ElectronicCats/CatFinder/Mechanics/SolidWorks/caramelo.SLDPRT

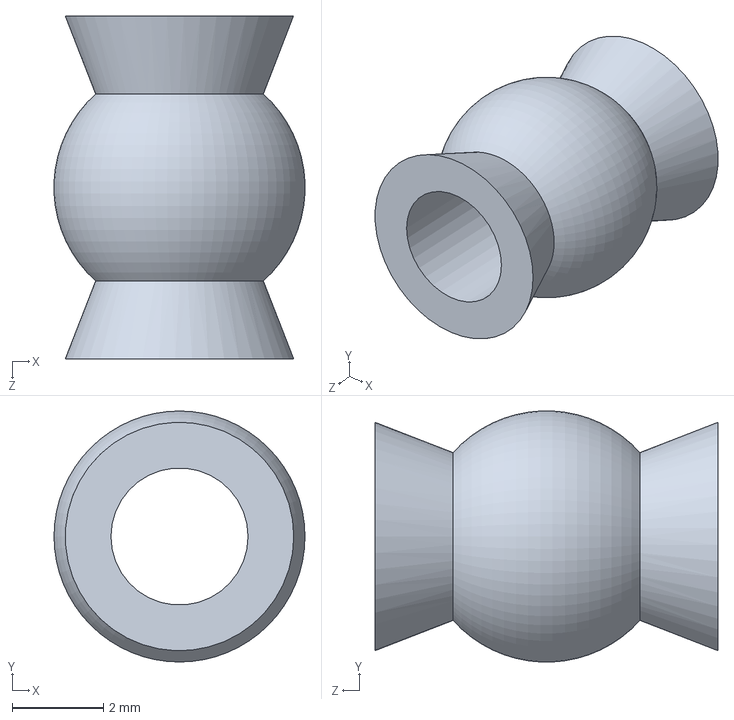
[picture p13: CAD file, 2019-09-29]
Mechanics/SolidWorks/caramelo.SLDPRT
5.49 x 5.49 x 7.50 mm
