ElectronicCats/CatFinder/Mechanics/SolidWorks/Acrilico frontal.SLDPRT

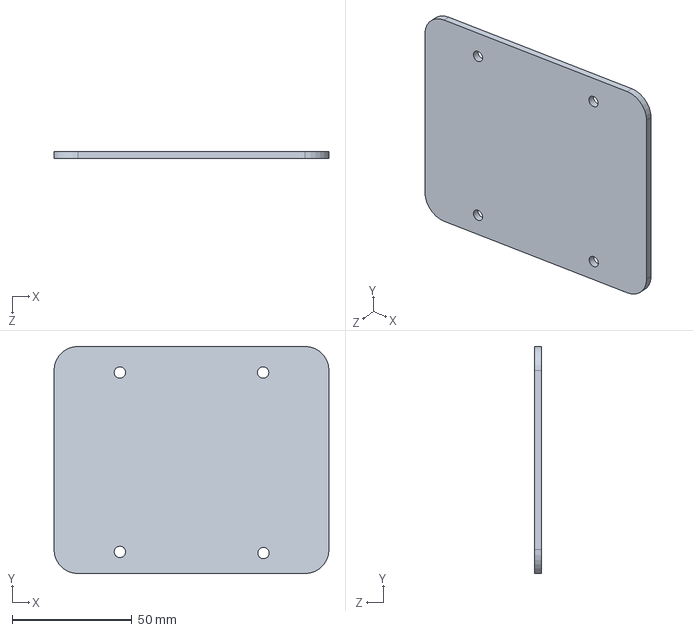
[picture p14: CAD file, 2019-09-29]
Mechanics/SolidWorks/Acrilico frontal.SLDPRT
115.0 x 95.0 x 3.00 mm
