ElectronicCats/CatFinder/Mechanics/SolidWorks/Soporte shf8.SLDPRT

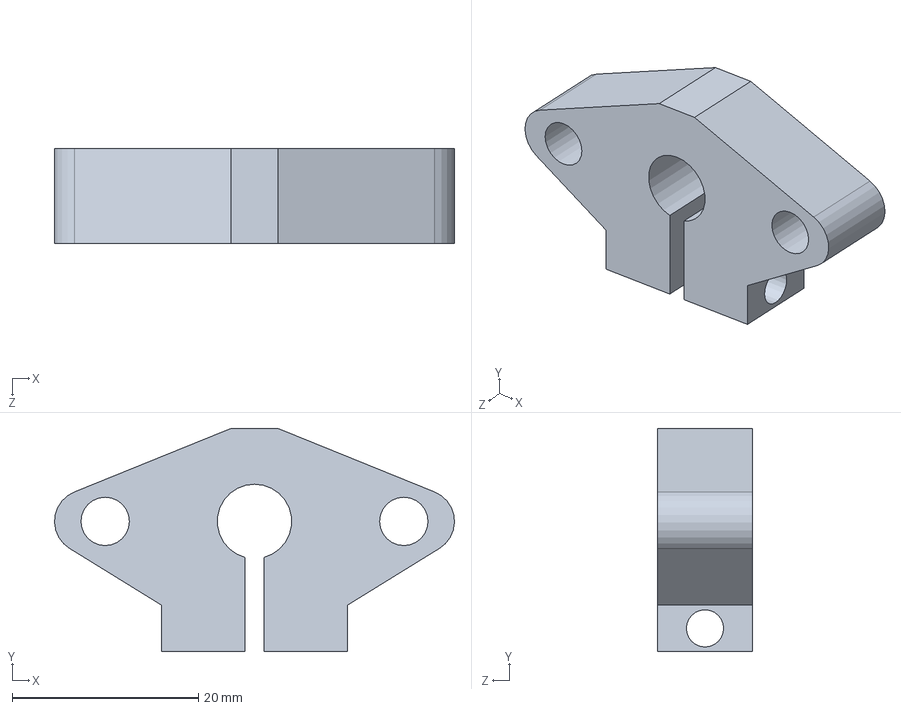
[picture p15: CAD file, 2019-09-29]
Mechanics/SolidWorks/Soporte shf8.SLDPRT
43.0 x 24.0 x 10.2 mm
