ElectronicCats/CatFinder/Mechanics/SolidWorks/Ajuste de rotulas.SLDPRT

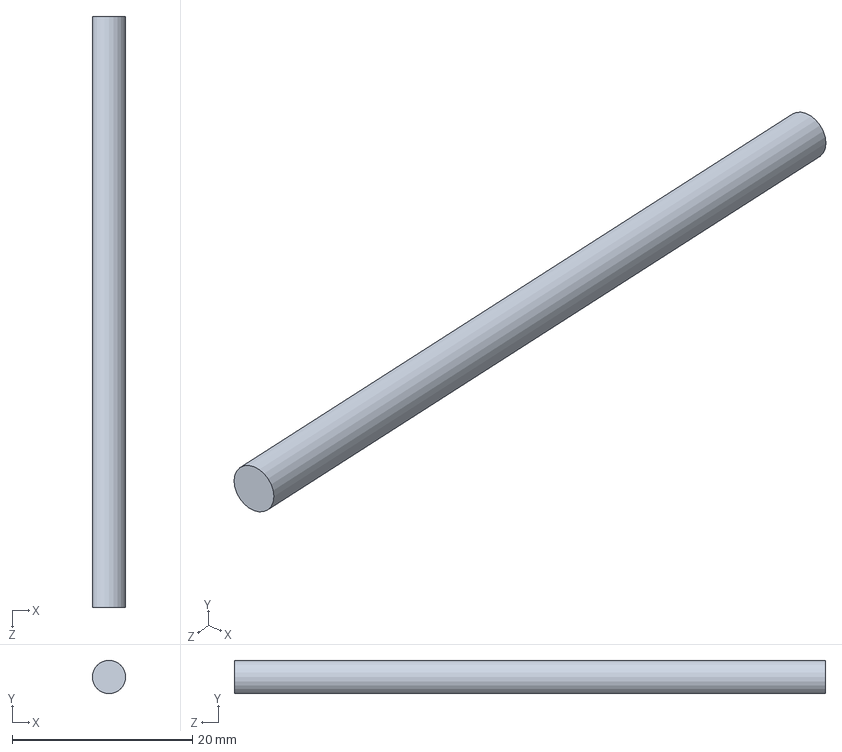
[picture p16: CAD file, 2019-09-29]
Mechanics/SolidWorks/Ajuste de rotulas.SLDPRT
3.70 x 3.70 x 65.5 mm
