ElectronicCats/CatFinder/Mechanics/SolidWorks/Balero 608.SLDPRT

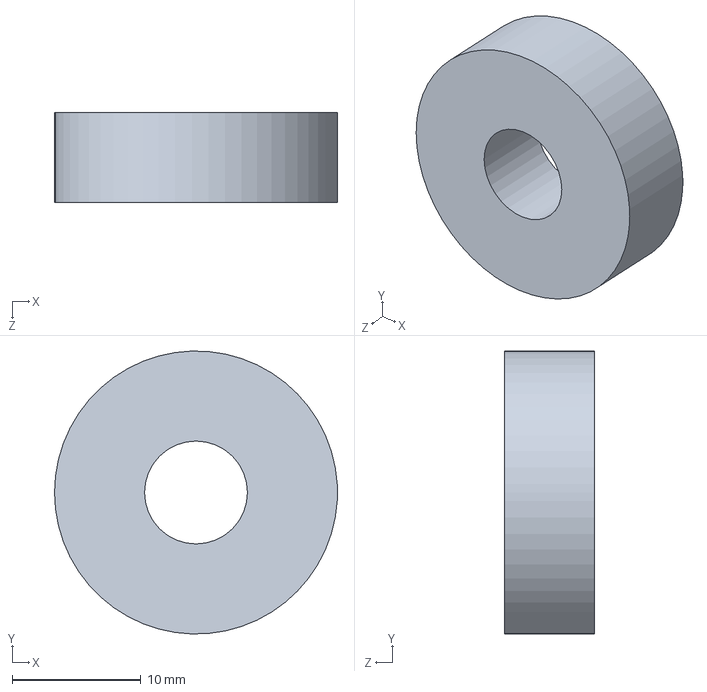
[picture p17: CAD file, 2019-09-29]
Mechanics/SolidWorks/Balero 608.SLDPRT
22.0 x 22.0 x 7.00 mm
