ElectronicCats/CatFinder/Mechanics/SolidWorks/Lamina para eje.SLDPRT

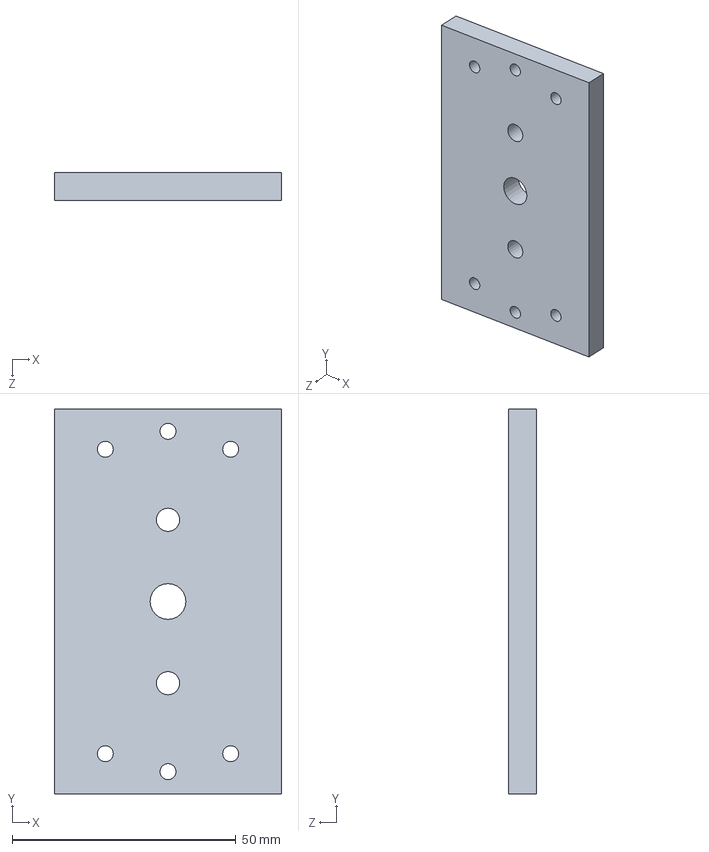
[picture p18: CAD file, 2019-09-29]
Mechanics/SolidWorks/Lamina para eje.SLDPRT
50.8 x 86.0 x 6.35 mm
