ElectronicCats/CatFinder/Mechanics/SolidWorks/motor.sldprt

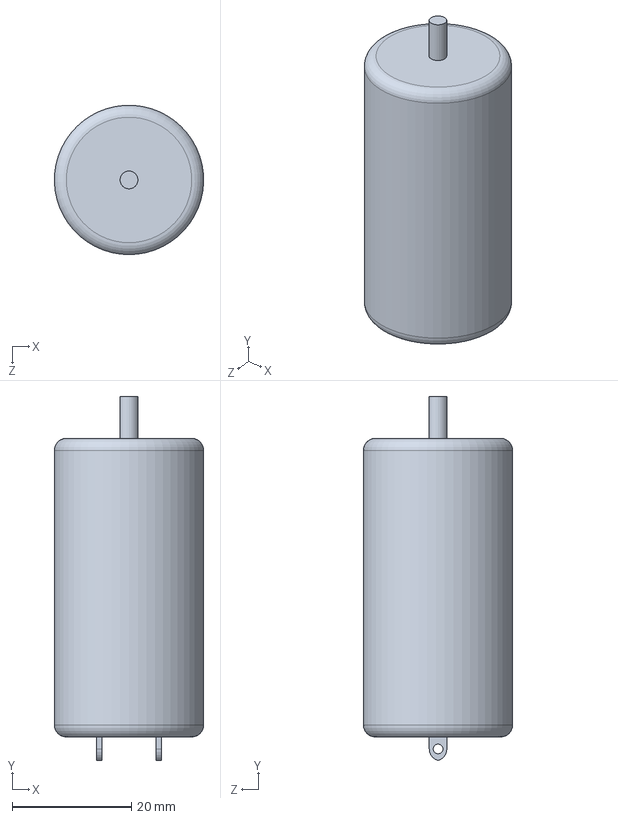
[picture p19: CAD file, 2019-09-29]
Mechanics/SolidWorks/motor.sldprt
25.0 x 60.9 x 25.0 mm
