ElectronicCats/CatFinder/Mechanics/SolidWorks/Soporte sk8.SLDPRT

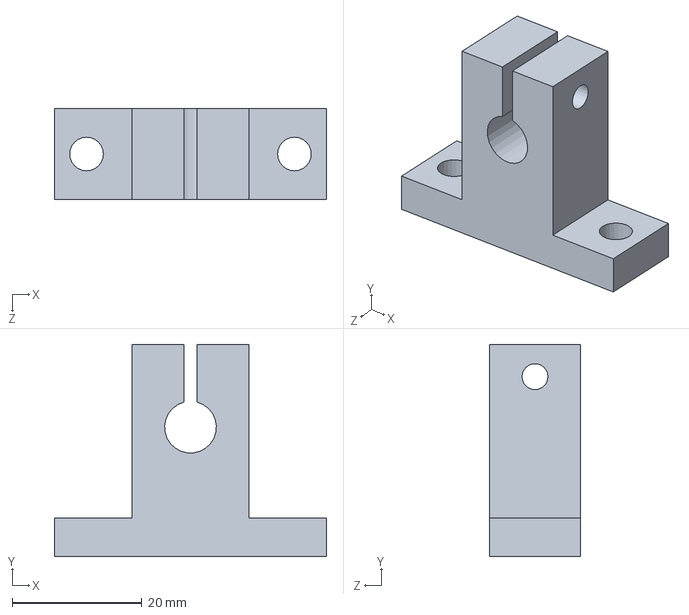
[picture p20: CAD file, 2019-09-29]
Mechanics/SolidWorks/Soporte sk8.SLDPRT
42.0 x 32.8 x 14.0 mm
