ElectronicCats/CatFinder/Mechanics/SolidWorks/Acrilico.SLDPRT

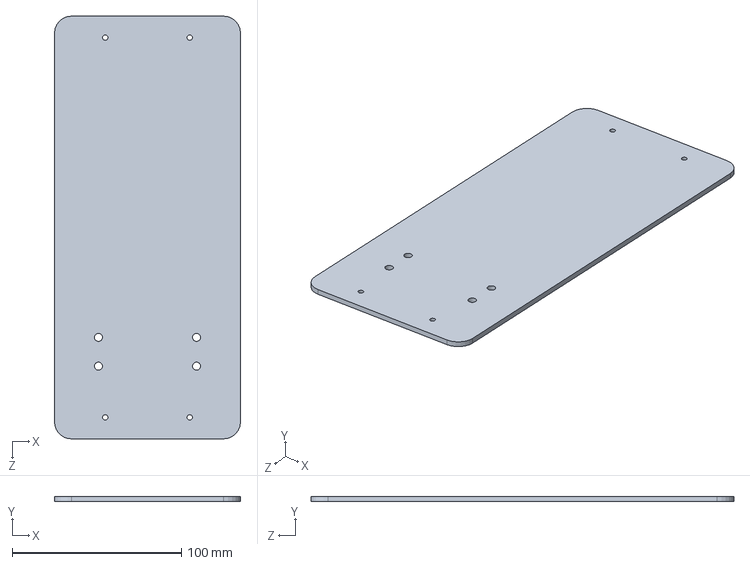
[picture p21: CAD file, 2019-09-29]
Mechanics/SolidWorks/Acrilico.SLDPRT
110.0 x 3.00 x 250.0 mm
