ElectronicCats/CatFinder/Mechanics/SolidWorks/Esquinas de Caja.SLDPRT

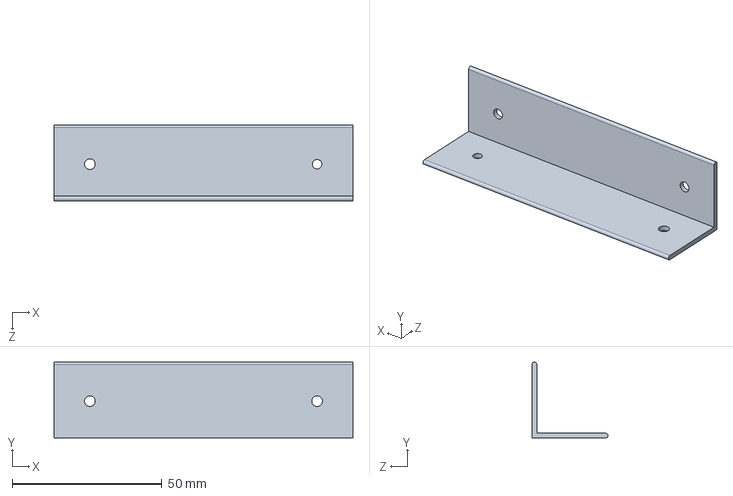
[picture p22: CAD file, 2019-09-29]
Mechanics/SolidWorks/Esquinas de Caja.SLDPRT
100.0 x 25.4 x 25.4 mm
