ElectronicCats/CatFinder/Mechanics/SolidWorks/Laterales de caja 1.SLDPRT

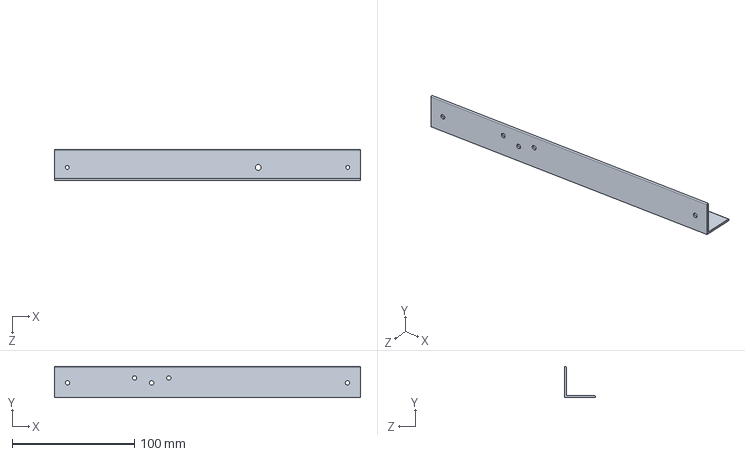
[picture p23: CAD file, 2019-09-29]
Mechanics/SolidWorks/Laterales de caja 1.SLDPRT
250.0 x 25.4 x 25.4 mm
