ElectronicCats/CatFinder/Mechanics/SolidWorks/Chumacera de pared.SLDPRT

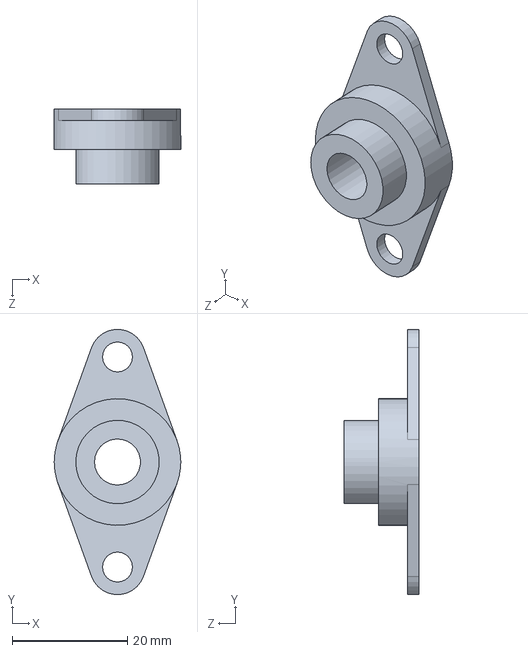
[picture p24: CAD file, 2019-09-29]
Mechanics/SolidWorks/Chumacera de pared.SLDPRT
22.0 x 46.0 x 13.0 mm
