ElectronicCats/CatFinder/Mechanics/SolidWorks/tubo 115mm 1.sldprt

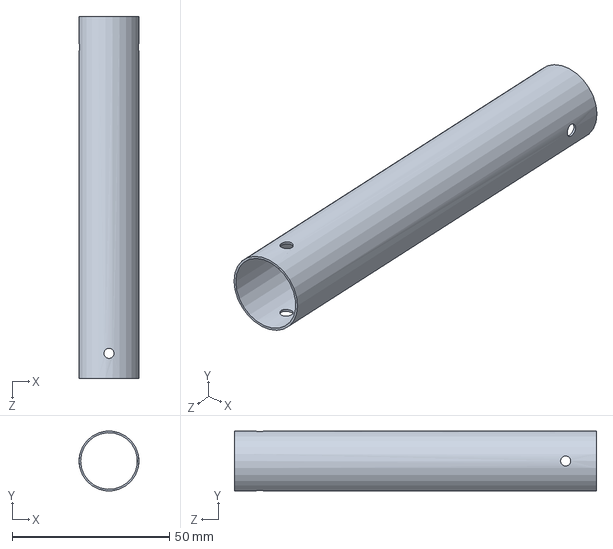
[picture p25: CAD file, 2019-09-29]
Mechanics/SolidWorks/tubo 115mm 1.sldprt
19.1 x 19.1 x 115.0 mm
