ElectronicCats/CatFinder/Mechanics/SolidWorks/Union Rotulas.SLDPRT

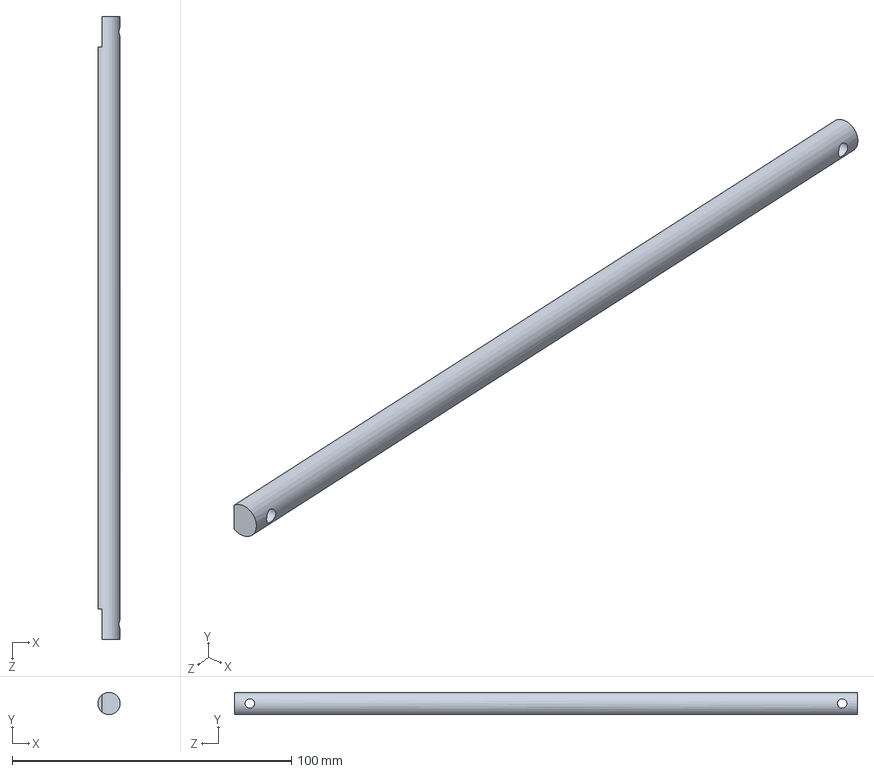
[picture p26: CAD file, 2019-09-29]
Mechanics/SolidWorks/Union Rotulas.SLDPRT
8.00 x 8.00 x 223.0 mm
