ElectronicCats/CatFinder/Mechanics/SolidWorks/Acrilico Base.SLDPRT

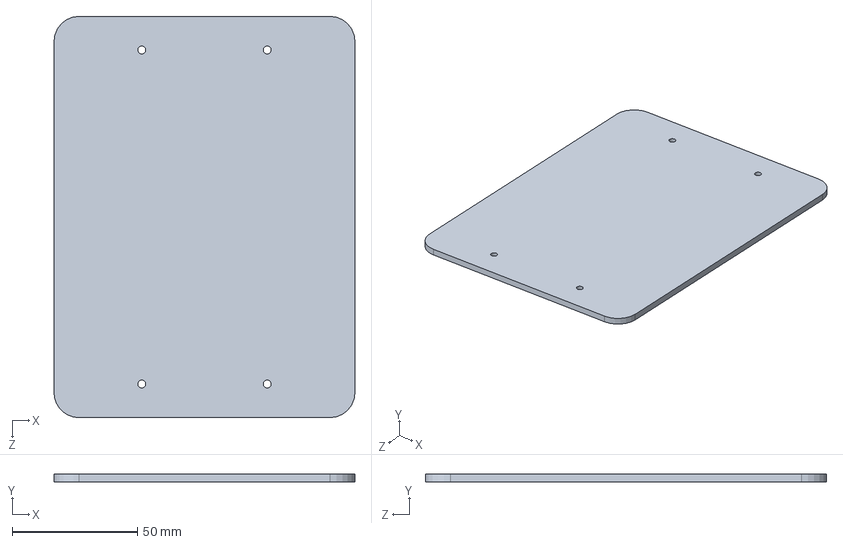
[picture p27: CAD file, 2019-09-29]
Mechanics/SolidWorks/Acrilico Base.SLDPRT
120.0 x 3.00 x 160.0 mm
