ElectronicCats/CatFinder/Mechanics/SolidWorks/Eje.SLDPRT

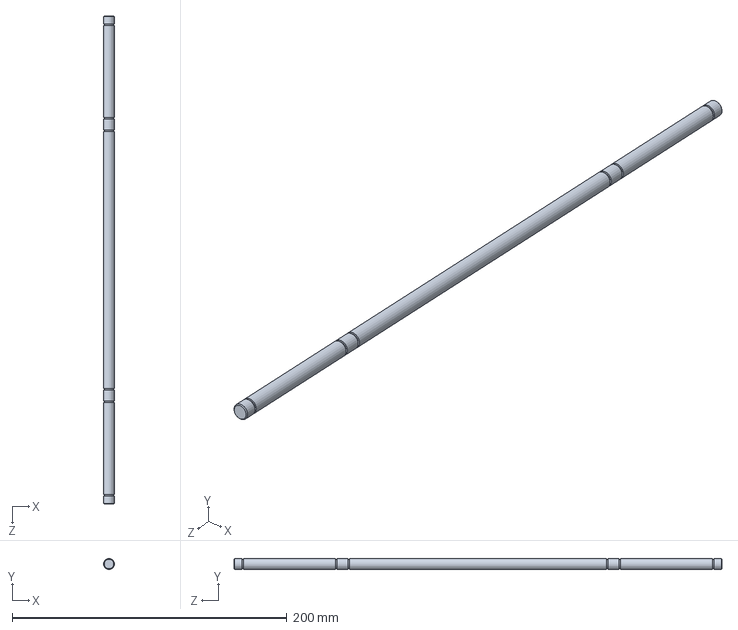
[picture p28: CAD file, 2019-09-29]
Mechanics/SolidWorks/Eje.SLDPRT
7.98 x 7.98 x 355.0 mm
