ElectronicCats/CatFinder/Mechanics/SolidWorks/Hook Spring.SLDPRT

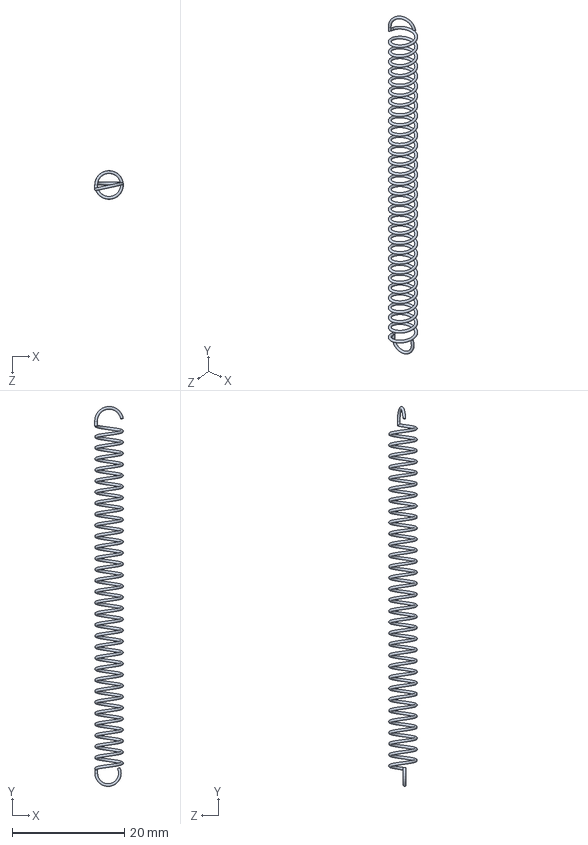
[picture p29: CAD file, 2019-09-29]
Mechanics/SolidWorks/Hook Spring.SLDPRT
5.12 x 67.6 x 5.10 mm
